stephengilliland/ACRS-Senior-Project/Project_ALK_Rev1/Alk_Rev1/Alk_Rev1.ino

#include <Wire.h>

int LED = 13;
int alk = 10;
int packetnum = 1;

void setup() {
  // put your setup code here, to run once:
  Wire.begin(7);                // join i2c bus with address #8
  Wire.onRequest(requestEvent); // register event
}

// function that executes whenever data is requested by master
// this function is registered as an event, see setup()

void requestEvent()
{
  
  if(packetnum == 1)
  {
    Wire.write("A"); // respond with
  }
  if(packetnum == 2)
  {
    Wire.write(alk);
  }
  packetnum = packetnum + 1;
  if(packetnum > 2)
    packetnum = 1;
    
  
  
  // as expected by master
}

void loop() {
  // put your main code here, to run repeatedly:

}
